gauthamdk/hourglass/images/shapes.png

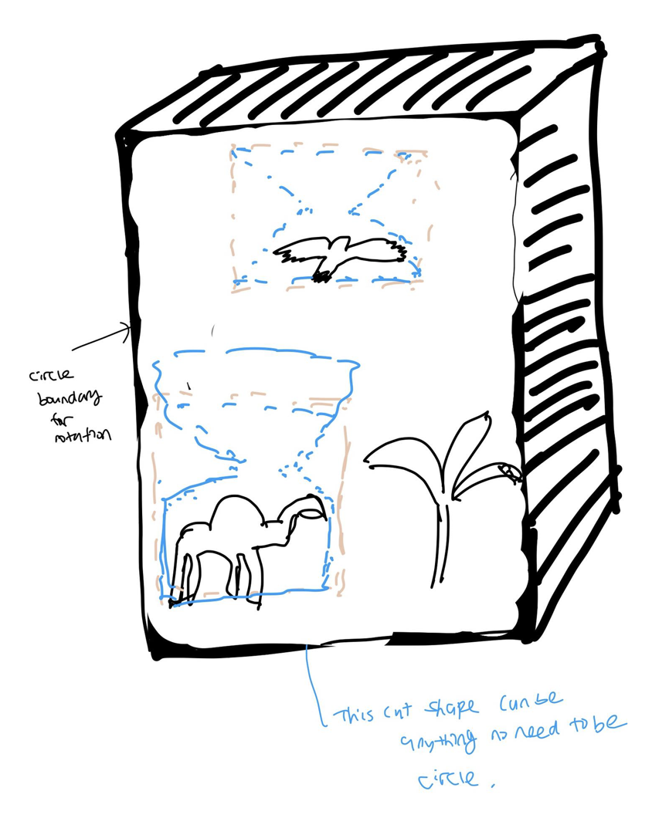
images/shapes.png
